zaeem7744/Plant-Sensor-Network/Schemetic/Plant_Sensor_Network/Plant_Sensor_Network.kicad_sch

## KiCad design Schemetic/Plant_Sensor_Network/Plant_Sensor_Network.kicad_sch (2026-02-23)

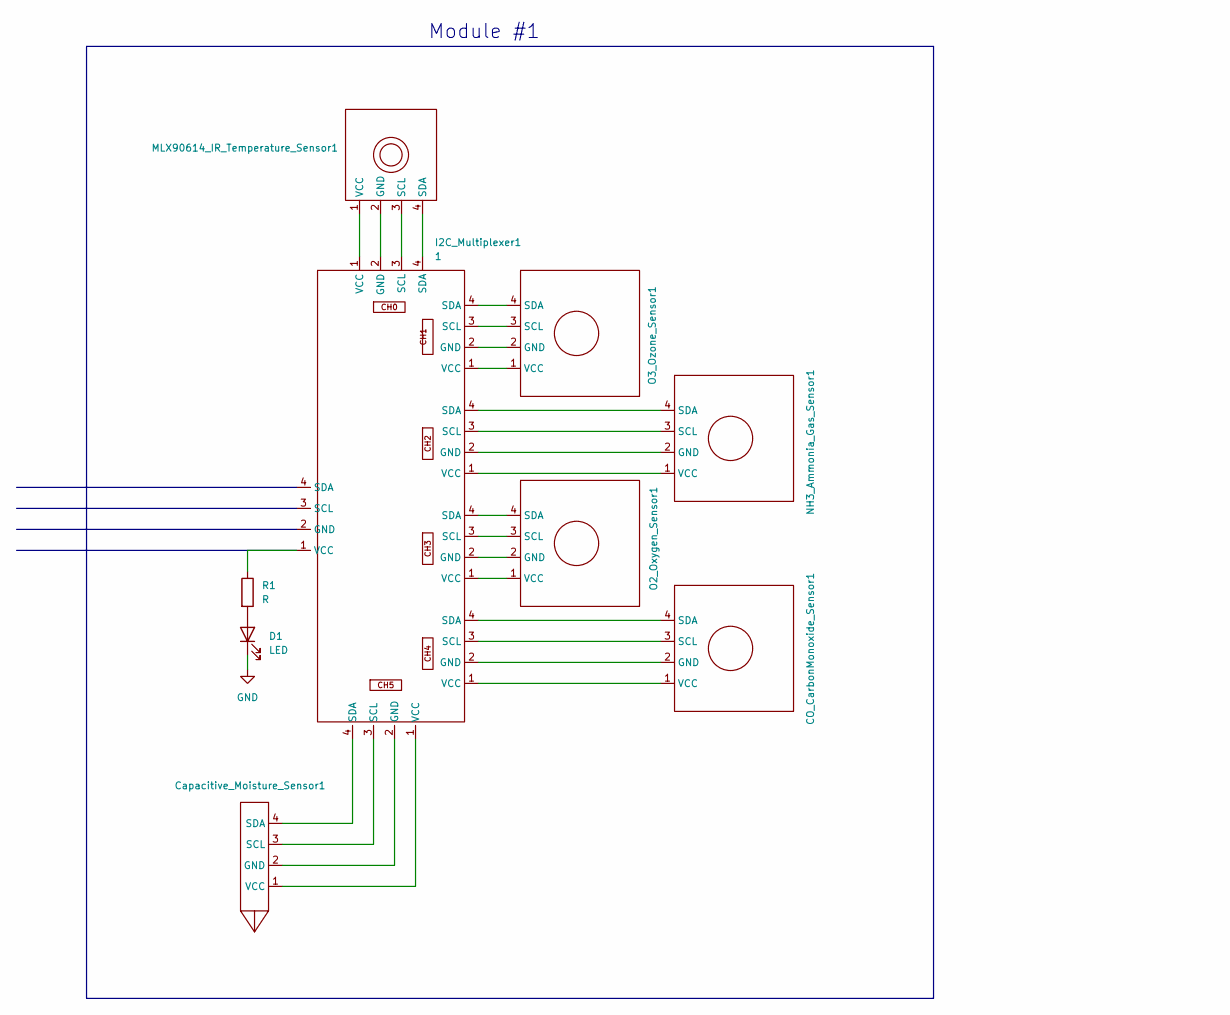
[picture p10: schematic Plant_Sensor_Network.kicad_sch, part in row 1, column 1]

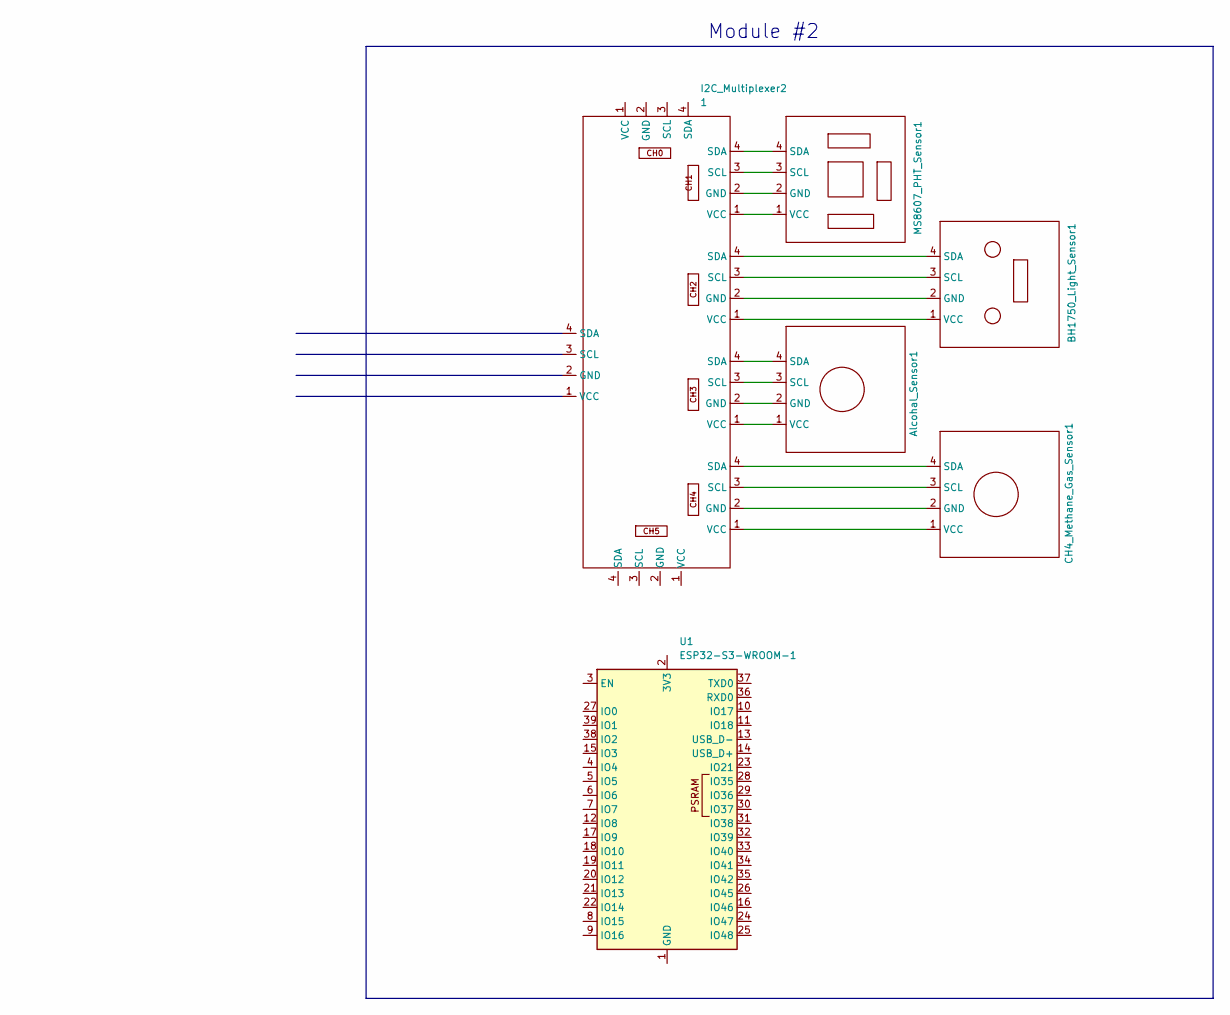
[picture p11: schematic Plant_Sensor_Network.kicad_sch, part in row 1, column 2]

Parts:
Alcohal_Sensor1: (no value)
BH1750_Light_Sensor1: (no value)
CH4_Methane_Gas_Sensor1: (no value)
CO_CarbonMonoxide_Sensor1: (no value)
Capacitive_Moisture_Sensor1: (no value)
D1: LED
I2C_Multiplexer1, I2C_Multiplexer2: 1
MLX90614_IR_Temperature_Sensor1: (no value)
MS8607_PHT_Sensor1: (no value)
NH3_Ammonia_Gas_Sensor1: (no value)
O2_Oxygen_Sensor1, O3_Ozone_Sensor1: (no value)
R1: R
U1: ESP32-S3-WROOM-1

Connections:
GND: D1.1 (K)
unnamed: Alcohal_Sensor1.1 (VCC), I2C_Multiplexer2.1 (VCC)
unnamed: Alcohal_Sensor1.2 (GND), I2C_Multiplexer2.2 (GND)
unnamed: Alcohal_Sensor1.3 (SCL), I2C_Multiplexer2.3 (SCL)
unnamed: Alcohal_Sensor1.4 (SDA), I2C_Multiplexer2.4 (SDA)
unnamed: BH1750_Light_Sensor1.1 (VCC), I2C_Multiplexer2.1 (VCC)
unnamed: BH1750_Light_Sensor1.2 (GND), I2C_Multiplexer2.2 (GND)
unnamed: BH1750_Light_Sensor1.3 (SCL), I2C_Multiplexer2.3 (SCL)
unnamed: BH1750_Light_Sensor1.4 (SDA), I2C_Multiplexer2.4 (SDA)
unnamed: CH4_Methane_Gas_Sensor1.1 (VCC), I2C_Multiplexer2.1 (VCC)
unnamed: CH4_Methane_Gas_Sensor1.2 (GND), I2C_Multiplexer2.2 (GND)
unnamed: CH4_Methane_Gas_Sensor1.3 (SCL), I2C_Multiplexer2.3 (SCL)
unnamed: CH4_Methane_Gas_Sensor1.4 (SDA), I2C_Multiplexer2.4 (SDA)
unnamed: CO_CarbonMonoxide_Sensor1.1 (VCC), I2C_Multiplexer1.1 (VCC)
unnamed: CO_CarbonMonoxide_Sensor1.2 (GND), I2C_Multiplexer1.2 (GND)
unnamed: CO_CarbonMonoxide_Sensor1.3 (SCL), I2C_Multiplexer1.3 (SCL)
unnamed: CO_CarbonMonoxide_Sensor1.4 (SDA), I2C_Multiplexer1.4 (SDA)
unnamed: Capacitive_Moisture_Sensor1.1 (VCC), I2C_Multiplexer1.1 (VCC)
unnamed: Capacitive_Moisture_Sensor1.2 (GND), I2C_Multiplexer1.2 (GND)
unnamed: Capacitive_Moisture_Sensor1.3 (SCL), I2C_Multiplexer1.3 (SCL)
unnamed: Capacitive_Moisture_Sensor1.4 (SDA), I2C_Multiplexer1.4 (SDA)
unnamed: D1.2 (A), R1.2
unnamed: I2C_Multiplexer1.1 (VCC), MLX90614_IR_Temperature_Sensor1.1 (VCC), NH3_Ammonia_Gas_Sensor1.1 (VCC), O2_Oxygen_Sensor1.1 (VCC), O3_Ozone_Sensor1.1 (VCC), R1.1
unnamed: I2C_Multiplexer1.2 (GND), MLX90614_IR_Temperature_Sensor1.2 (GND), NH3_Ammonia_Gas_Sensor1.2 (GND), O2_Oxygen_Sensor1.2 (GND), O3_Ozone_Sensor1.2 (GND)
unnamed: I2C_Multiplexer1.3 (SCL), MLX90614_IR_Temperature_Sensor1.3 (SCL), NH3_Ammonia_Gas_Sensor1.3 (SCL), O2_Oxygen_Sensor1.3 (SCL), O3_Ozone_Sensor1.3 (SCL)
unnamed: I2C_Multiplexer1.4 (SDA), MLX90614_IR_Temperature_Sensor1.4 (SDA), NH3_Ammonia_Gas_Sensor1.4 (SDA), O2_Oxygen_Sensor1.4 (SDA), O3_Ozone_Sensor1.4 (SDA)
unnamed: I2C_Multiplexer2.1 (VCC), MS8607_PHT_Sensor1.1 (VCC)
unnamed: I2C_Multiplexer2.2 (GND), MS8607_PHT_Sensor1.2 (GND)
unnamed: I2C_Multiplexer2.3 (SCL), MS8607_PHT_Sensor1.3 (SCL)
unnamed: I2C_Multiplexer2.4 (SDA), MS8607_PHT_Sensor1.4 (SDA)
unnamed: U1.1 (GND), U1.40 (GND), U1.41 (GND)

Notes on the sheet:
Module #2
Module #1
