zaeem7744/Plant-Sensor-Network/Firmware/Plant Sensor Network/config.h

#pragma once

// WiFi credentials
#define WIFI_SSID     "TP-Link_5F74"
#define WIFI_PASSWORD "73060420"

// Backend ingest URL (Python server on local network)
// Example: http://192.168.0.23:8000/api/ingest
#define BACKEND_URL   "http://192.168.1.105:8000/api/ingest"
